IronJulo/Bikeeper/3D_Models/Support_7x.SLDPRT

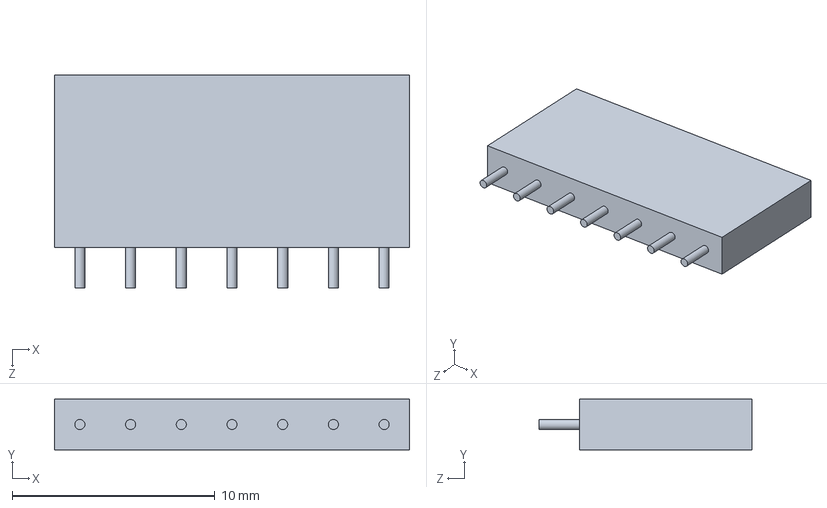
[picture p21: CAD file, 2021-03-18]
3D_Models/Support_7x.SLDPRT
17.5 x 2.50 x 10.5 mm
