IronJulo/Bikeeper/3D_Models/Arduino_Nano.SLDPRT

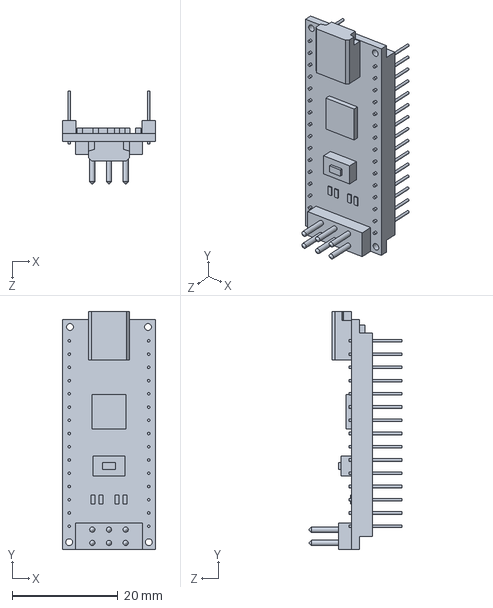
[picture p22: CAD file, 2021-03-18]
3D_Models/Arduino_Nano.SLDPRT
17.5 x 45.0 x 17.5 mm
