IronJulo/Bikeeper/3D_Models/Support_5x.SLDPRT

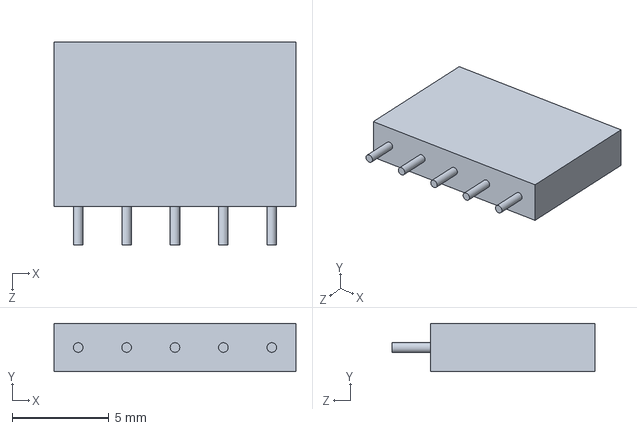
[picture p23: CAD file, 2021-03-18]
3D_Models/Support_5x.SLDPRT
12.5 x 2.50 x 10.5 mm
