IronJulo/Bikeeper/3D_Models/Support_15x.SLDPRT

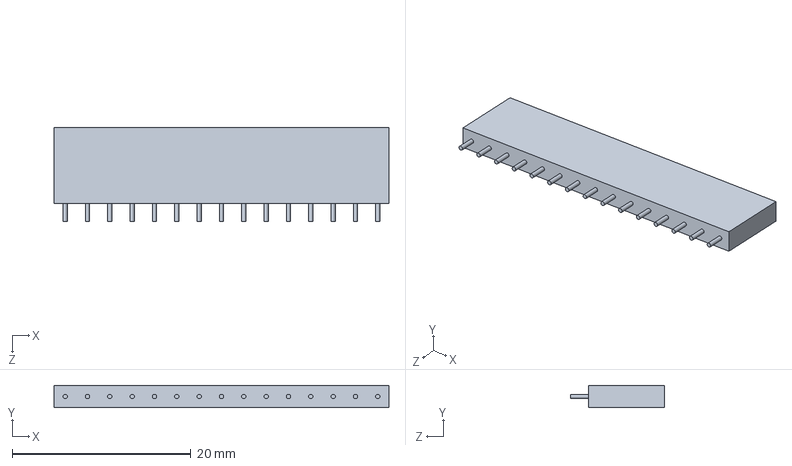
[picture p24: CAD file, 2021-03-18]
3D_Models/Support_15x.SLDPRT
37.5 x 2.50 x 10.5 mm
