IronJulo/Bikeeper/3D_Models/Resistor.SLDPRT

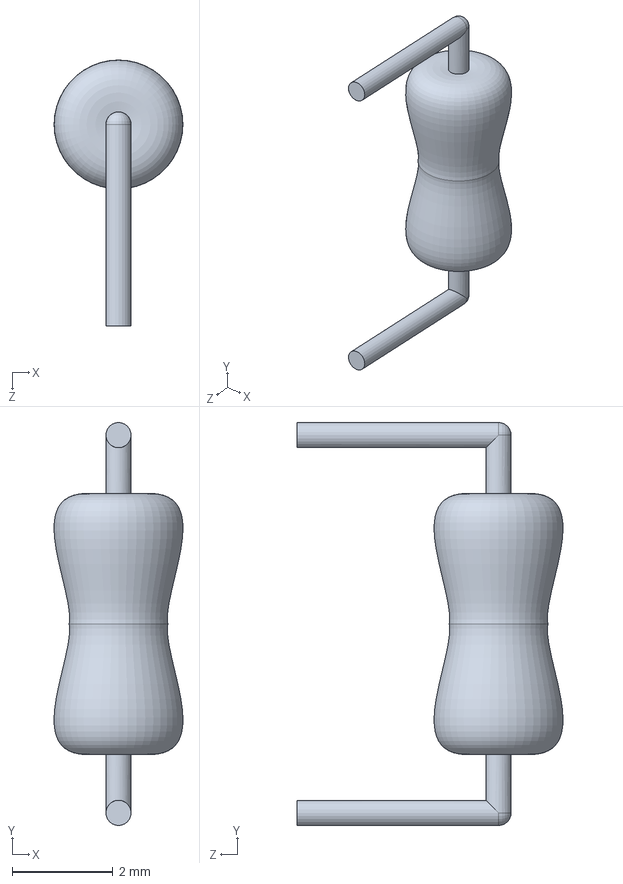
[picture p25: CAD file, 2021-03-18]
3D_Models/Resistor.SLDPRT
2.56 x 8.00 x 5.28 mm
