IronJulo/Bikeeper/3D_Models/Chargeur_Li-ion.SLDPRT

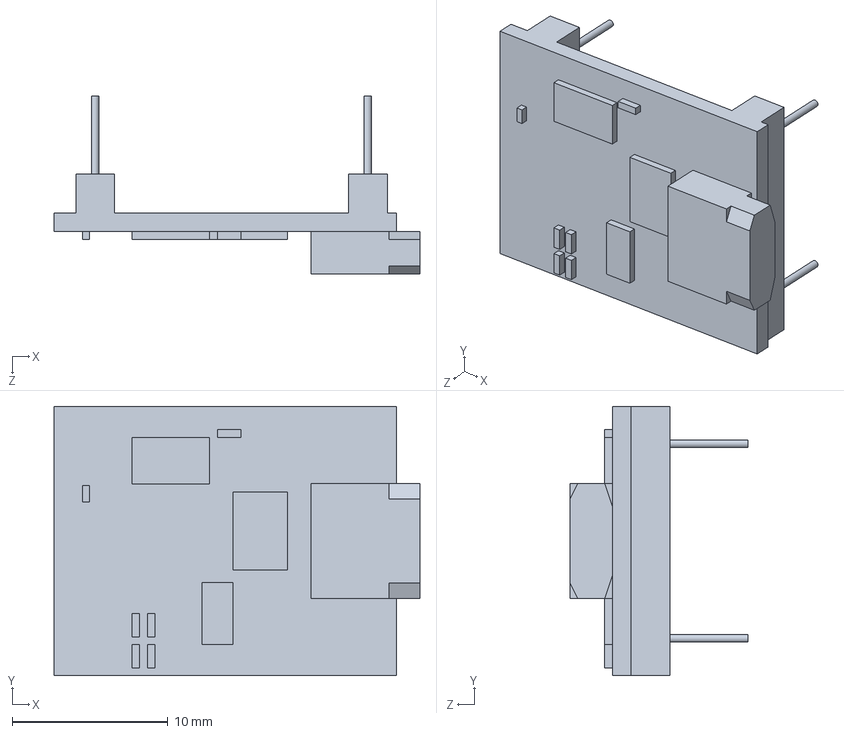
[picture p26: CAD file, 2021-03-18]
3D_Models/Chargeur_Li-ion.SLDPRT
23.5 x 17.3 x 11.4 mm
