IronJulo/Bikeeper/Arduino/server/AlertSendProtocol.py

from decimal import Decimal

class AlertSend:

    def __init__(self, data):
        self.data = data
        self.type = ""
        self.long = 0
        self.lat = 0
        self.charge = False
        self.lvl = [0,0]

    def get_data(self):
        return self.data

    def get_type(self):
        return self.type

    def get_long(self):
        return self.long

    def get_lat(self):
        return self.lat

    def get_charge(self):
        return self.charge

    def get_lvl(self):
        return self.lvl

    def set_data(self, data):
        self.data = data

    def set_type(self, alert_type):
        self.type = alert_type

    def set_long(self, long):
        self.long = long

    def set_lat(self, lat):
        self.lat = lat

    def set_charge(self, charge):
        self.charge = charge

    def set_lvl(self, lvl):
        self.lvl = lvl

    def auto_set(self):
        self.type = self.data[2]
        self.long = (Decimal(self.data[3])*1000).normalize()
        self.lat = (Decimal(self.data[4])*1000).normalize()
        self.charge = self.data[5]
        self.lvl[0] = int(self.data[6])
        self.lvl[1] = int(self.data[7])


    def to_dico(self):
        d = {}
        self.auto_set()
        d["type"]=self.get_type()
        d["longitude"]=float(self.get_long())
        d["latitude"]=float(self.get_lat())
        d["charge"]=self.get_charge()
        d["level"]=self.get_lvl()
        return d
